mkmatlock/spectrometer/images/cfl_reference_with_labels.png

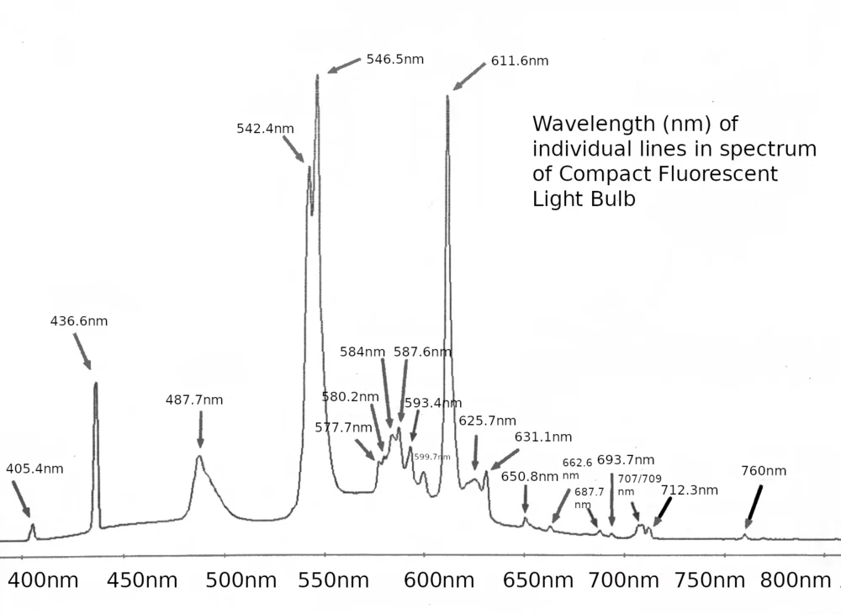
images/cfl_reference_with_labels.png
