mkmatlock/spectrometer/images/second order.png

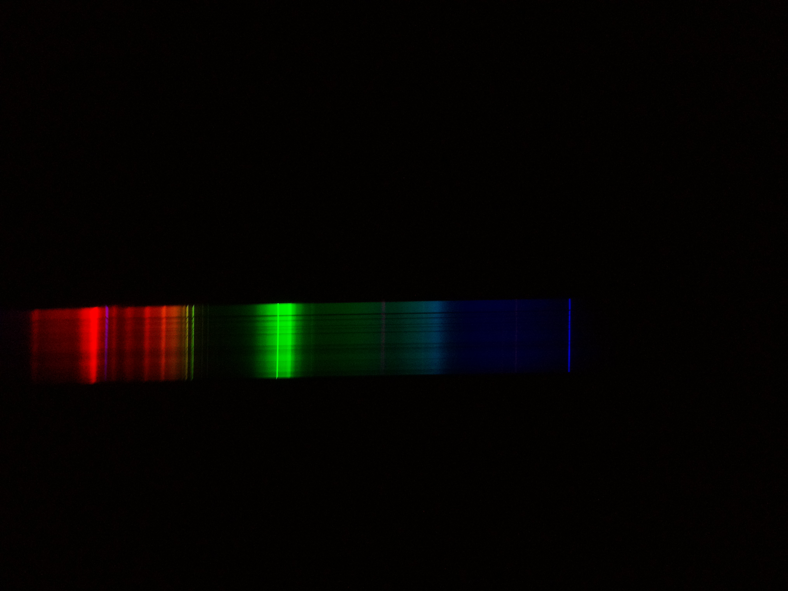
images/second order.png
