mkmatlock/spectrometer/models/Slit Stabilizer.3mf

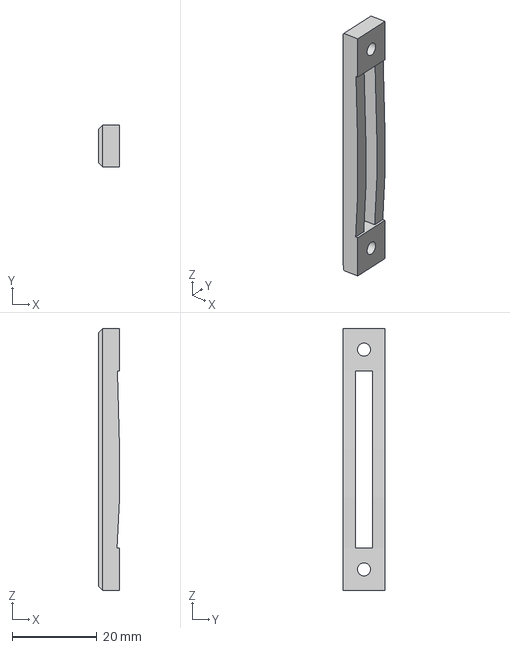
[picture p22: CAD file, 2026-09-16]
models/Slit Stabilizer.3mf
5.00 x 10.0 x 62.0 mm
