mkmatlock/spectrometer/models/Slit Mount.3mf

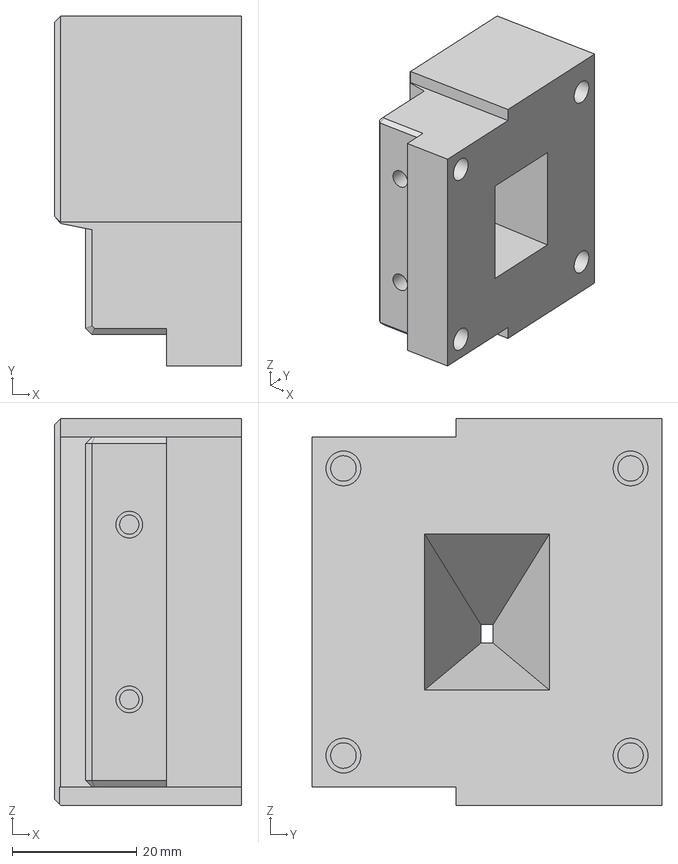
[picture p23: CAD file, 2026-09-16]
models/Slit Mount.3mf
30.0 x 56.0 x 62.0 mm
