mkmatlock/spectrometer/models/Microcontroller.3mf

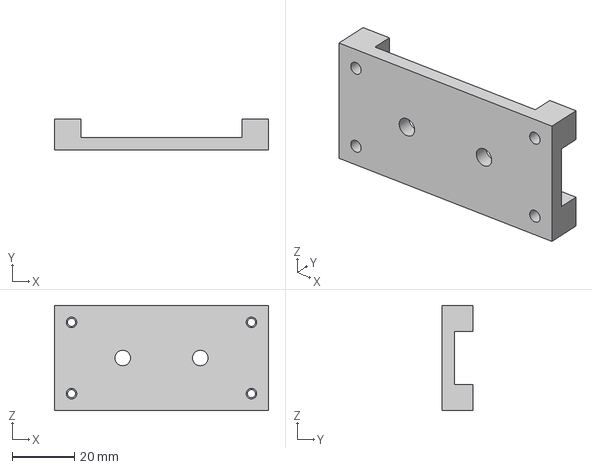
[picture p24: CAD file, 2026-09-16]
models/Microcontroller.3mf
69.0 x 10.0 x 34.0 mm
