mkmatlock/spectrometer/models/Interface.3mf

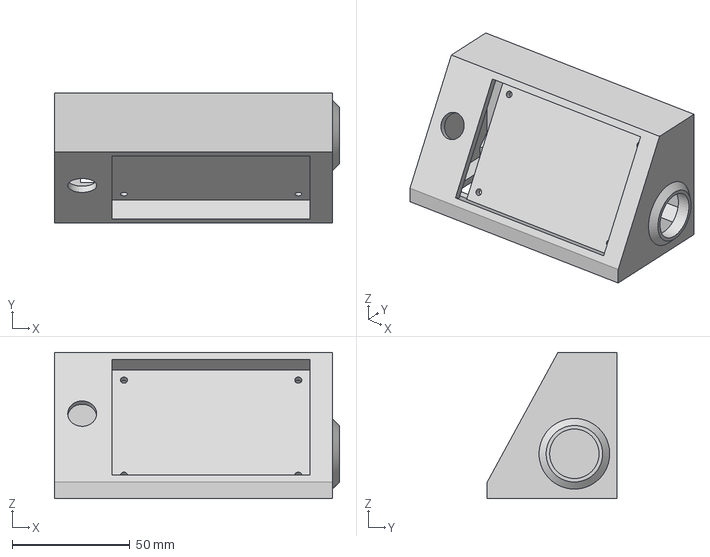
[picture p25: CAD file, 2026-09-16]
models/Interface.3mf
121.0 x 55.0 x 62.0 mm
