mkmatlock/spectrometer/images/build_bottom.jpg

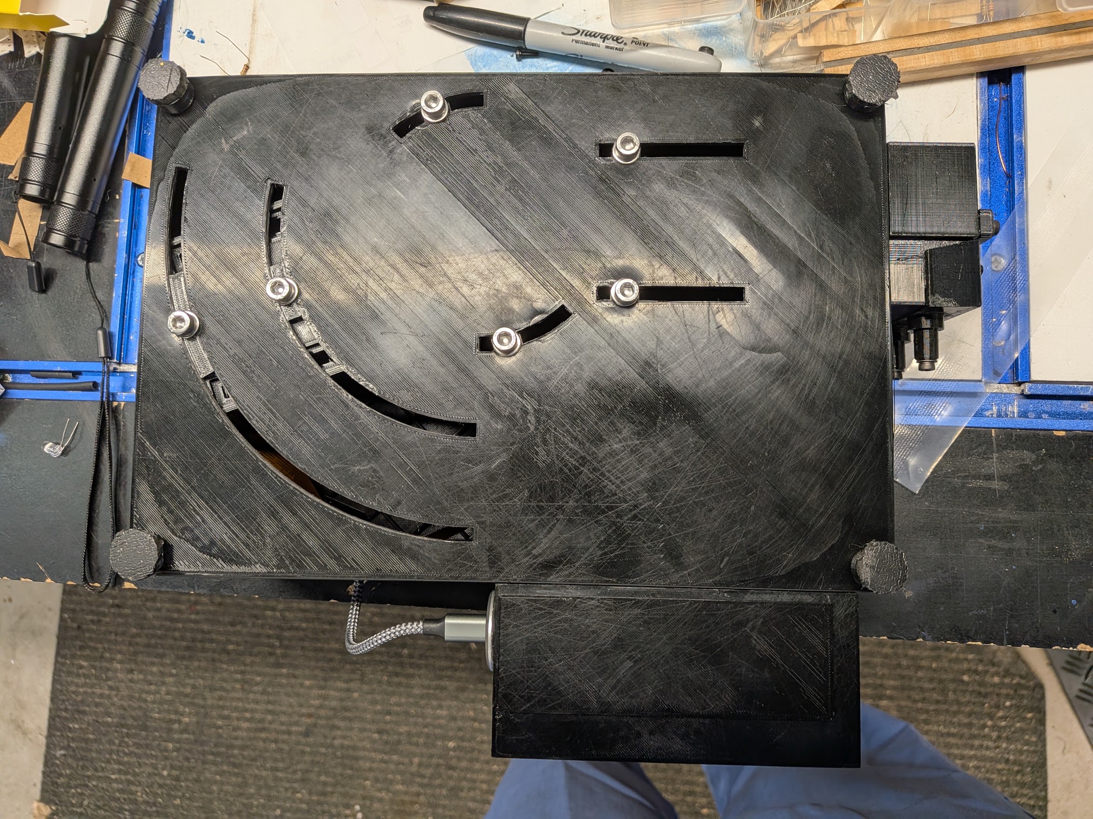
images/build_bottom.jpg
