mkmatlock/spectrometer/images/build_inside.jpg

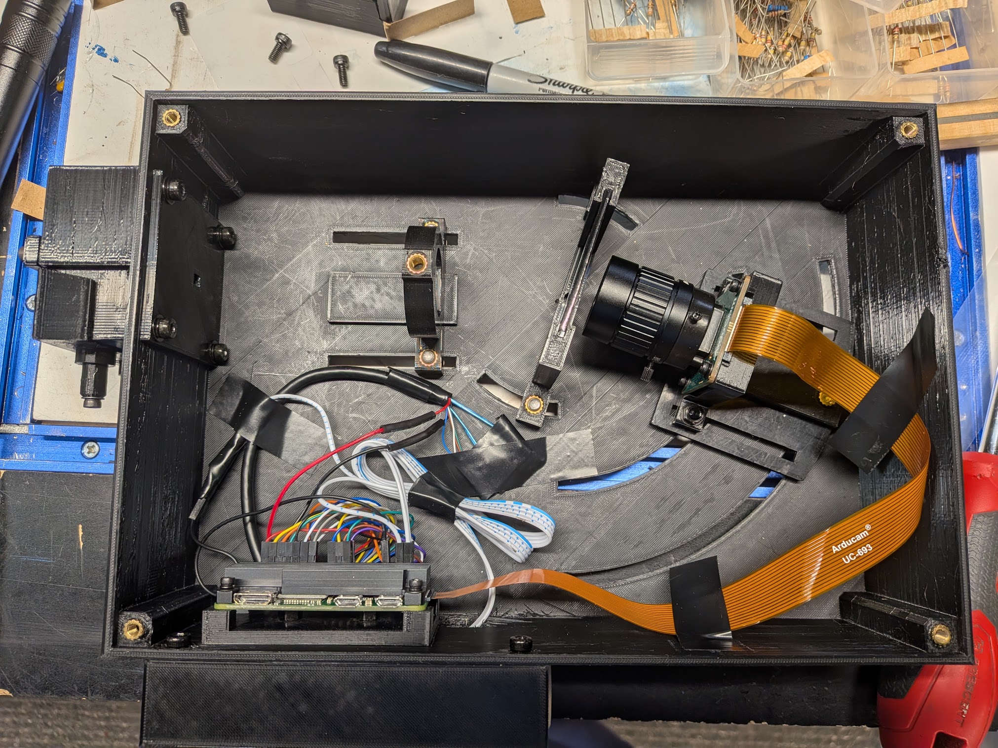
images/build_inside.jpg
