mkmatlock/spectrometer/images/build_lid_inside.jpg

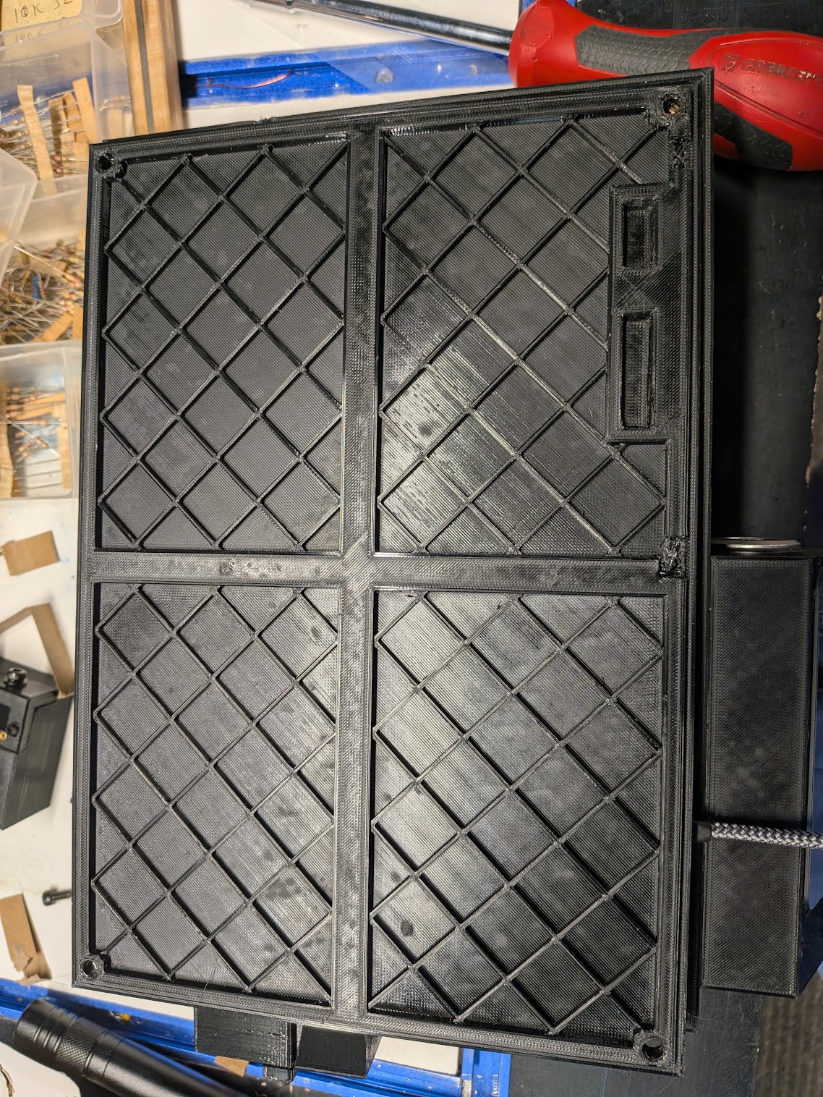
images/build_lid_inside.jpg
