mkmatlock/spectrometer/images/build_ports.jpg

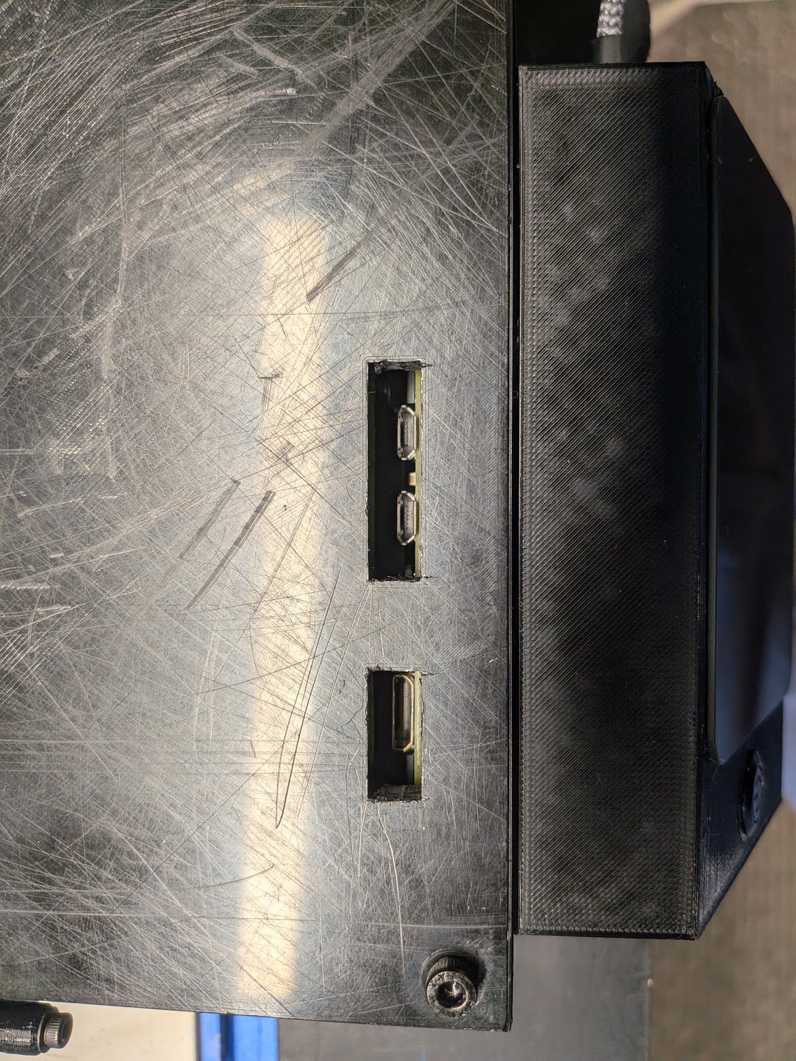
images/build_ports.jpg
