mkmatlock/spectrometer/images/build_slit.jpg

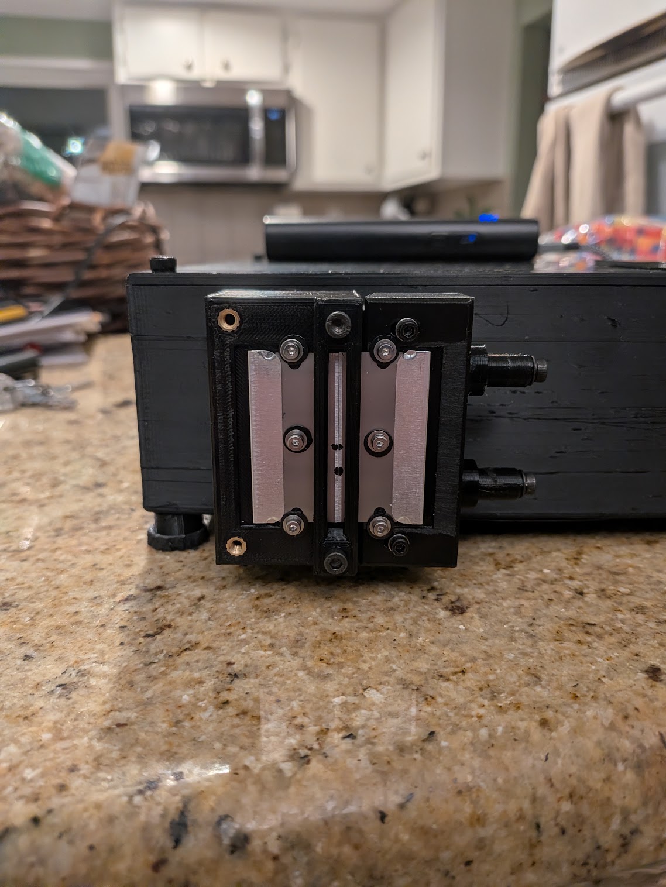
images/build_slit.jpg
