mkmatlock/spectrometer/tests/test_settings.py

import unittest
from unittest.mock import Mock, patch

from spectrometer.camera import CameraStream
from spectrometer.settings import SettingsView, network_status
from spectrometer.ui import SpectrometerUI


class SettingsTests(unittest.TestCase):
    def test_network_values_and_missing_tools(self):
        with patch('spectrometer.settings._output', side_effect=['192.168.1.42 fe80::1', 'Lab WiFi']):
            self.assertEqual(network_status(), ('192.168.1.42', 'Lab WiFi'))
        with patch('spectrometer.settings._output', side_effect=['192.168.1.42', None, '*:Lab:WiFi']):
            self.assertEqual(network_status(), ('192.168.1.42', 'Lab:WiFi'))
        with patch('spectrometer.settings._output', return_value=None):
            self.assertEqual(network_status(), ('Unavailable', 'Not connected / unavailable'))

    def test_settings_navigation_and_background_network(self):
        camera = Mock()
        camera.settings_snapshot.return_value = {'frame_rate': 5.0, 'resolution': (4056, 3040),
                                                 'exposure_us': 20000, 'frame_averaging': 3}
        ui = SpectrometerUI(camera=camera)
        try:
            with patch('spectrometer.settings.network_status', return_value=('10.0.0.2', 'Lab')):
                ui._open_settings()
                ui.settings_view.future.result(timeout=5)
                ui._poll_settings()
            self.assertEqual(ui.mode, 'settings')
            self.assertEqual(ui.settings_view.rows, [('Frame rate', '5 fps'),
                             ('Camera resolution', '4056 x 3040'), ('Exposure time', '20 ms'),
                             ('Frame averaging', '3'),
                             ('IP address', '10.0.0.2'), ('Wi-Fi network', 'Lab')])
            self.assertFalse(ui._poll_camera())
            ui._pointer_event('lcd', (40, 50), True)
            ui._pointer_event('lcd', (40, 50), False)
            self.assertEqual(ui.mode, 'settings')
            self.assertEqual(ui._settings_dialog, 'frame_rate')
            ui.buttons[1][2]()
            ui.buttons[0][2]()
            self.assertTrue(ui._calibration_dialog)
            ui.buttons[1][2]()
            self.assertEqual(ui.mode, 'settings')
            ui.buttons[1][2]()
            self.assertEqual(ui.mode, 'live')
            camera.request_pause.assert_called_once_with()
            camera.request_resume.assert_called_once_with()
        finally:
            ui.review.close()
            ui.settings_view.close()

    def test_edit_camera_settings_and_reconfigure_on_exit(self):
        camera = Mock()
        changes = []
        calibration = {'scale': {100: 500.0}, 'sensor_area': (0, 100, 1000, 200),
                       'channel_ranges': {'Red': (0, 999)}}
        ui = SpectrometerUI(
            camera=camera,
            camera_settings={'frame_rate': 5.0, 'resolution': (4056, 3040),
                             'exposure_us': None, 'frame_averaging': 3},
            calibration_settings=calibration,
            on_camera_settings_changed=lambda values, calibration=None:
            changes.append((values.copy(), calibration)))
        try:
            with patch('spectrometer.settings.network_status', return_value=('10.0.0.2', 'Lab')):
                ui._open_settings()

            ui._edit_setting(0)
            self.assertEqual((ui._settings_min, ui._settings_max), (-3, 5))
            ui._settings_value = 5
            ui._accept_setting()

            ui._edit_setting(2)
            self.assertEqual((ui._settings_min, ui._settings_max), (0, 201))
            ui._settings_value = 25
            ui._accept_setting()

            ui._edit_setting(3)
            self.assertEqual((ui._settings_min, ui._settings_max), (1, 10))
            ui._settings_value = 10
            ui._accept_setting()

            ui._edit_setting(1)
            ui._resolution_selected = 1
            ui._accept_setting()
            self.assertEqual(ui._camera_settings['resolution'], (2028, 1520))
            self.assertEqual(ui.calibration_settings,
                             {'scale': {}, 'sensor_area': (0, 0, 2028, 1520),
                              'channel_ranges': {}})
            self.assertEqual(ui.settings_view.rows[0:4],
                             [('Frame rate', '5 fps'),
                              ('Camera resolution', '2028 x 1520'),
                              ('Exposure time', '25 ms'), ('Frame averaging', '10')])

            ui._exit_settings()
            configured = camera.request_reconfigure.call_args.args[0]
            self.assertEqual(configured.resolution, (2028, 1520))
            self.assertEqual(configured.roi, (0, 0, 2028, 1520))
            self.assertEqual(configured.frame_averaging, 10)
            self.assertEqual(len(changes), 4)
            camera.request_resume.assert_not_called()
        finally:
            ui.review.close()
            ui.settings_view.close()

    def test_slow_frame_rates_round_trip_and_exposure_limit(self):
        ui = SpectrometerUI()
        try:
            for seconds in (2, 3, 4, 5):
                ui._edit_setting(0)
                track = ui._setting_slider_rect()
                position = 2 - seconds
                x = track.left + (position - ui._settings_min) / (ui._settings_max - ui._settings_min) * track.width
                ui._set_slider_position((x, track.centery))
                ui._accept_setting()
                self.assertAlmostEqual(ui._camera_settings['frame_rate'], 1 / seconds)
                self.assertEqual(ui.settings_view.rows[0], ('Frame rate', f'{seconds} spf'))
                ui._edit_setting(0)
                self.assertEqual(ui._settings_value, position)
                ui._cancel_setting()
                ui._edit_setting(2)
                self.assertEqual(ui._settings_max, seconds * 1000 + 1)
                ui._cancel_setting()
        finally:
            ui.review.close()
            ui.settings_view.close()

    def test_exposure_modes_and_fixed_values_across_frame_rates(self):
        camera = Mock()
        camera.exposure_limits.side_effect = lambda fps, resolution: (114, min(900000, int(1000000 / fps)))
        from spectrometer.config import DEFAULTS
        ui = SpectrometerUI(camera=camera, camera_settings=DEFAULTS['camera'])
        try:
            def change_rate(position):
                ui._edit_setting(0)
                ui._settings_value = position
                ui._accept_setting()

            for mode in ('min', 'max'):
                ui._edit_setting(2)
                ui._settings_value = ui._exposure_options.index(mode)
                ui._accept_setting()
                for position in (1, 5, -3):
                    change_rate(position)
                    self.assertEqual(ui._camera_settings['exposure_us'], mode)
                    self.assertEqual(ui.settings_view.rows[2], ('Exposure time', mode.title()))
                    ui._edit_setting(2)
                    self.assertEqual(ui._exposure_options[ui._settings_value], mode)
                    ui._cancel_setting()

            for previous, expected in ((25000, 25000), (500000, 200000), (10, 114)):
                ui._camera_settings['exposure_us'] = previous
                change_rate(5)
                self.assertEqual(ui._camera_settings['exposure_us'], expected)
                change_rate(1)
                self.assertEqual(ui._camera_settings['exposure_us'], expected)
                # Opening and accepting must preserve exact microseconds.
                ui._edit_setting(2)
                ui._accept_setting()
                self.assertEqual(ui._camera_settings['exposure_us'], expected)
        finally:
            ui.review.close()
            ui.settings_view.close()

    def test_snapshot_uses_actual_frame_timing_and_exposure(self):
        camera = CameraStream()
        try:
            camera._frame_duration_us = 250000
            camera._exposure_us = 12345
            self.assertEqual(camera.settings_snapshot(), {'frame_rate': 4.0,
                             'resolution': (4056, 3040), 'exposure_us': 12345,
                             'frame_averaging': 3})
        finally:
            camera.close()

    def test_calibration_dialog_selection_and_modal_input(self):
        ui = SpectrometerUI()
        try:
            with patch('spectrometer.settings.network_status', return_value=('Unavailable', 'Unavailable')):
                ui._open_settings()
                ui.settings_view.future.result(timeout=5)
            ui._calibrate()
            self.assertEqual([b[0] for b in ui.buttons], ['Select', 'Back'])
            self.assertEqual([r[0] for r in ui._calibration_rows],
                             ['Background', 'Sensor', 'Scale', 'Channel'])
            ui._select_calibration()
            self.assertIn('Choose', ui._calibration_message)
            for index, (name, rect) in enumerate(ui._calibration_rows[:1]):
                ui._pointer_event('lcd', rect.center, True)
                ui._pointer_event('lcd', rect.center, False)
                self.assertEqual(ui._calibration_selected, index)
                ui._select_calibration()
                self.assertEqual(ui._calibration_message, name + ': not implemented yet')
            ui._pointer_event('lcd', (350, 300), True)
            ui._pointer_event('lcd', (350, 300), False)
            self.assertTrue(ui._calibration_dialog)  # Underlying Settings Back is blocked.
            ui._back_calibration()
            self.assertFalse(ui._calibration_dialog)
            self.assertEqual(ui.mode, 'settings')
            self.assertEqual([b[0] for b in ui.buttons], ['Calibrate', 'Back'])
        finally:
            ui.review.close()
            ui.settings_view.close()
