mkmatlock/spectrometer/tests/test_review.py

from datetime import datetime, timezone
from pathlib import Path
import pickle
from copy import deepcopy
import tempfile
import unittest
from unittest.mock import Mock, patch

import numpy as np
import pygame

from spectrometer.camera import BAR_SIZE
from spectrometer.capture import save_capture
from spectrometer.review import ReviewList, load_spectrum, raw_rgb
from spectrometer.ui import SpectrometerUI
from tests.spectrum_fixtures import spectrum_record


def record(second=0):
    return spectrum_record(
        timestamp=datetime(2026, 9, 12, 12, 0, second, tzinfo=timezone.utc),
        spectrum_intensity=np.arange(3500, dtype=np.int32),
        spectrum_bar=bytes((255, 0, 0)) * (BAR_SIZE[0] * BAR_SIZE[1]))


class ReviewTests(unittest.TestCase):
    def test_delete_modal_cancel_confirm_and_exact_loaded_file(self):
        with tempfile.TemporaryDirectory() as directory:
            older = save_capture(record(0), directory)
            newest = save_capture(record(1), directory)
            ui = SpectrometerUI(review_directory=directory)
            try:
                ui._open_review()
                ui.review.selected = 0
                ui.review.display()
                ui.review.future.result(timeout=5)
                ui.review.selected = 1  # Selection changes must not change delete target.
                ui._poll_review()
                def tap(position):
                    ui._pointer_event('lcd', position, True)
                    ui._pointer_event('lcd', position, False)
                tap((80, 280))
                self.assertTrue(ui._delete_dialog)
                self.assertTrue(newest.exists())
                tap((350, 280))  # Back behind the modal must not receive input.
                self.assertTrue(ui._delete_dialog)
                tap((330, 190))
                self.assertFalse(ui._delete_dialog)
                self.assertEqual(ui.mode, 'saved')
                self.assertTrue(newest.exists())
                tap((80, 280))
                tap((150, 190))
                self.assertFalse(newest.exists())
                self.assertTrue(older.exists())
                self.assertEqual(ui.mode, 'review')
                self.assertFalse(ui._delete_dialog)
                self.assertEqual(ui.review.entries, [older])
            finally:
                ui.review.close()
                ui.settings_view.close()

    def test_delete_failure_keeps_file_and_dialog_open(self):
        with tempfile.TemporaryDirectory() as directory:
            path = save_capture(record(), directory)
            ui = SpectrometerUI(review_directory=directory)
            try:
                ui._open_review()
                ui.review.selected = 0
                ui.review.display()
                ui.review.future.result(timeout=5)
                ui._poll_review()
                ui._ask_delete()
                with patch.object(Path, 'unlink', side_effect=PermissionError('Read only')):
                    ui._confirm_delete()
                self.assertTrue(path.exists())
                self.assertTrue(ui._delete_dialog)
                self.assertIn('Delete failed', ui._delete_message)
            finally:
                ui.review.close()
                ui.settings_view.close()

    def test_newest_first_scroll_and_empty_list(self):
        with tempfile.TemporaryDirectory() as directory:
            review = ReviewList(directory)
            try:
                review.refresh()
                self.assertEqual(review.entries, [])
                review.display()
                self.assertEqual(review.message, 'Select a capture first')
                for second in range(8):
                    save_capture(record(second), directory)
                review.refresh()
                self.assertTrue(review.entries[0].name.endswith('07.pkl'))
                review.scroll(100)
                self.assertEqual(review.offset, 3)
                review.scroll(-100)
                self.assertEqual(review.offset, 0)
            finally:
                review.close()

    def test_select_display_back_exit_and_live_isolation(self):
        with tempfile.TemporaryDirectory() as directory:
            save_capture(record(), directory)
            camera = Mock()
            ui = SpectrometerUI(camera=camera, review_directory=directory)
            try:
                original = ui._plot
                ui._open_review()
                camera.request_pause.assert_called_once()
                self.assertFalse(ui._poll_camera())
                camera.poll.assert_not_called()
                ui._pointer_event('lcd', (50, 50), True)
                ui._pointer_event('lcd', (50, 50), False)
                ui.buttons[0][2]()
                ui.review.future.result(timeout=5)
                ui._poll_review()
                self.assertEqual(ui.mode, 'saved')
                self.assertEqual([b[0] for b in ui.buttons], ['Delete', 'Modes', 'Back'])
                self.assertEqual(ui._camera_bar.get_at((0, 0))[:3], (255, 0, 0))
                ui.buttons[2][2]()
                self.assertEqual(ui.mode, 'review')
                self.assertEqual(ui.review.selected, 0)
                ui.buttons[2][2]()
                self.assertEqual(ui.mode, 'live')
                self.assertIs(ui._plot, original)
                camera.request_resume.assert_called_once()
            finally:
                ui.review.close()

    def test_swipe_scroll_does_not_select(self):
        ui = SpectrometerUI()
        try:
            ui._open_review()
            ui.review.entries = [Path(str(i)) for i in range(12)]
            ui._pointer_event('lcd', (50, 220), True)
            ui._pointer_motion('lcd', (50, 90))
            ui._pointer_event('lcd', (50, 90), False)
            self.assertEqual(ui.review.offset, 3)
            self.assertIsNone(ui.review.selected)
        finally:
            ui.review.close()

    def test_bad_pickle_shows_error_and_stays_in_list(self):
        with tempfile.TemporaryDirectory() as directory:
            path = Path(directory) / 'spectrum-broken.pkl'
            path.write_bytes(b'broken')
            review = ReviewList(directory)
            try:
                review.refresh()
                review.selected = 0
                review.display()
                try:
                    review.future.result(timeout=5)
                except Exception:
                    pass
                self.assertIsNone(review.poll())
                self.assertTrue(review.message.startswith('Cannot load:'))
            finally:
                review.close()

    def test_averaged_bgr_roi_decodes_without_changing_saved_image(self):
        data = record()
        data['averaged_camera_output'][:] = (10, 20, 30)
        result = raw_rgb(data)
        self.assertEqual(result.shape, (250, 3500, 3))
        np.testing.assert_array_equal(result[0, 0], [30, 20, 10])
        np.testing.assert_array_equal(data['averaged_camera_output'][0, 0], [10, 20, 30])

    def test_invalid_spectrum_rejected(self):
        with tempfile.TemporaryDirectory() as directory:
            data = record()
            data['spectrum_intensity'] = np.zeros(10)
            path = save_capture(data, directory)
            with self.assertRaises(ValueError):
                load_spectrum(path)

    def test_plot_requires_saved_roi_bar_maximum_and_nested_calibration(self):
        data = spectrum_record(spectrum_roi=(0, 0, 462, 2))
        fields = [('spectrum_roi',), ('spectrum_bar',), ('spectrum_maximum',),
                  ('instrument_settings', 'calibration_settings')]
        with tempfile.TemporaryDirectory() as directory:
            path = Path(directory) / 'spectrum-test.pkl'
            for field in fields:
                with self.subTest(field=field):
                    invalid = deepcopy(data)
                    target = invalid
                    for part in field[:-1]:
                        target = target[part]
                    del target[field[-1]]
                    path.write_bytes(pickle.dumps(invalid))
                    with self.assertRaises(KeyError):
                        load_spectrum(path)

    def test_channel_processing_requires_averaged_roi_metadata(self):
        data = spectrum_record(spectrum_roi=(0, 0, 462, 2))
        fields = [('averaged_camera_output',),
                  ('instrument_settings', 'averaged_camera_format'),
                  ('instrument_settings', 'averaged_camera_format', 'size'),
                  ('instrument_settings', 'averaged_camera_format', 'origin'),
                  ('instrument_settings', 'averaged_camera_format', 'format')]
        for field in fields:
            with self.subTest(field=field):
                invalid = deepcopy(data)
                target = invalid
                for part in field[:-1]:
                    target = target[part]
                del target[field[-1]]
                with self.assertRaises(KeyError):
                    raw_rgb(invalid)

    def test_saved_maximum_controls_plot_independently_of_calculation_metadata(self):
        values = np.zeros(462, np.int32)
        values[100] = 500
        data = spectrum_record(spectrum_roi=(0, 0, 462, 2),
                               spectrum_intensity=values, spectrum_maximum=500)
        with tempfile.TemporaryDirectory() as directory:
            path = Path(directory) / 'spectrum-test.pkl'
            ui = SpectrometerUI(review_directory=directory)
            try:
                ui.mode = 'saved'
                for calculation in ('rgb_channel_sum', 'unrecognized', None):
                    with self.subTest(calculation=calculation):
                        if calculation is None:
                            data['instrument_settings'].pop('intensity_calculation')
                        else:
                            data['instrument_settings']['intensity_calculation'] = calculation
                        path.write_bytes(pickle.dumps(data))
                        frame = load_spectrum(path)
                        ui._update_plot(frame)
                        self.assertEqual(frame.maximum, 500)
                        self.assertEqual(ui._plot.maximum, 500)
                        self.assertEqual(min(point[1] for point in ui._plot.points),
                                         ui._plot.AREA.top)
                        np.testing.assert_array_equal(frame.intensity, values)
            finally:
                ui.review.close()
                ui.settings_view.close()
