mkmatlock/spectrometer/tests/test_scale.py

import pickle
from copy import deepcopy
from pathlib import Path
import tempfile
import unittest
from unittest.mock import Mock, patch

import numpy as np
import pygame

from spectrometer.scale import PeakSelection, peak_indices
from spectrometer.config import DEFAULTS, SettingsStore
from spectrometer.ui import SpectrometerUI
from tests.spectrum_fixtures import spectrum_record


class ScaleTests(unittest.TestCase):
    def test_reset_requires_confirmation_and_only_clears_draft(self):
        with tempfile.TemporaryDirectory() as directory:
            store = SettingsStore(Path(directory) / '.spectrometer_config')
            store.update(calibration={'scale': {1000: 500.0, 2500: 700.0}})
            ui = SpectrometerUI(
                calibration_settings=deepcopy(store.data['calibration']),
                on_calibration_changed=lambda data: store.update(calibration=data))
            try:
                ui.mode = 'saved'
                ui._scale_active = True
                ui._saved_buttons = []
                original = deepcopy(ui.calibration_settings)
                ui._reset_scale()
                self.assertTrue(ui._scale_reset_dialog)
                self.assertEqual(ui._scale_labels, original['scale'])
                with patch.object(ui, '_select_peak') as select:
                    ui._pointer_event('lcd', (100, 100), True)
                    ui._pointer_event('lcd', (100, 100), False)
                    select.assert_not_called()
                ui._cancel_scale_reset()
                self.assertFalse(ui._scale_reset_dialog)
                self.assertEqual(ui._scale_labels, original['scale'])
                self.assertIs(ui.buttons, ui._saved_buttons)
                ui._reset_scale()
                ui._confirm_scale_reset()
                self.assertFalse(ui._scale_reset_dialog)
                self.assertEqual(ui._scale_labels, {})
                self.assertEqual(ui.calibration_settings, original)
                self.assertEqual(SettingsStore(store.path).data['calibration'], original)
            finally:
                ui.review.close()
                ui.settings_view.close()

    def test_absorption_plateau_valleys_and_toggle_in_scale(self):
        np.testing.assert_array_equal(peak_indices([9, 2, 2, 2, 9, 3, 9], absorption=True), [2, 5])
        ui = SpectrometerUI()
        try:
            ui.mode = 'saved'
            ui._scale_active = True
            values = np.full(3500, 50000, dtype=np.int32)
            values[1200] = 10000
            ui._plot.update(values)
            ui._reset_peaks(values)
            ui._saved_buttons = [('Accept', pygame.Rect(8, 264, 110, 48), ui._finish_scale),
                                 ('Reset', pygame.Rect(126, 264, 110, 48), ui._reset_scale),
                                 ('Modes', pygame.Rect(244, 264, 110, 48), ui._ask_filter),
                                 ('Back', pygame.Rect(362, 264, 110, 48), ui._cancel_scale)]
            ui._ask_filter()
            ui._choose_filter('Emission')
            self.assertEqual(ui.buttons[3][0], 'Absorption')
            self.assertTrue(ui._filter_dialog)
            np.testing.assert_array_equal(ui._peaks.indices, [1200])
            ui._back_filter()
            ui._select_peak(ui._peaks.positions[0])
            self.assertEqual(ui._peak_message, 'Pixel 1200')
            self.assertEqual([b[0] for b in ui.buttons], ['Label', 'Back'])
            ui._back_peak()
            self.assertEqual([b[0] for b in ui.buttons], ['Accept', 'Reset', 'Modes', 'Back'])
            ui._ask_filter()
            ui._choose_filter('Absorption')
            self.assertFalse(ui._absorption)
            self.assertIsNone(ui._peaks.marker)
        finally:
            ui.review.close()
            ui.settings_view.close()

    def test_plateaus_and_flat_spectra(self):
        np.testing.assert_array_equal(peak_indices([0, 2, 2, 2, 0, 3, 0]), [2, 5])
        self.assertEqual(len(peak_indices(np.zeros(3500))), 0)
        self.assertEqual(len(peak_indices(np.arange(3500))), 0)

    def test_nearest_peak_uses_screen_distance(self):
        values = np.zeros(3500)
        values[1000], values[2500] = 50000, 30000
        peaks = PeakSelection(values, pygame.Rect(9, 36, 462, 130), 63750)
        self.assertEqual(peaks.select(peaks.positions[1] + (2, 4)), 2500)
        self.assertEqual(peaks.marker, tuple(np.rint(peaks.positions[1]).astype(int)))

    def test_scale_capture_selection_peak_dialog_and_return(self):
        with tempfile.TemporaryDirectory() as directory:
            path = Path(directory) / 'spectrum-2026-09-13-12-00-00.pkl'
            values = np.zeros(3500, dtype=np.int32)
            values[1000], values[2500] = 50000, 30000
            original = pickle.dumps(spectrum_record(spectrum_intensity=values))
            path.write_bytes(original)
            camera = Mock()
            camera.settings_snapshot.return_value = deepcopy(DEFAULTS['camera'])
            ui = SpectrometerUI(camera=camera, review_directory=directory)
            try:
                with patch('spectrometer.settings.network_status', return_value=('Unavailable', 'Unavailable')):
                    ui._open_settings()
                    ui.settings_view.future.result(timeout=5)
                ui._calibrate()
                ui._calibration_selected = 2
                ui._select_calibration()
                self.assertEqual(ui.mode, 'review')
                self.assertTrue(ui._scale_active)
                self.assertFalse(ui._calibration_dialog)
                ui.review.selected = 0
                ui.review.display()
                ui.review.future.result(timeout=5)
                ui._poll_review()
                self.assertEqual(ui.mode, 'saved')
                self.assertEqual([b[0] for b in ui.buttons], ['Accept', 'Reset', 'Modes', 'Back'])
                position = tuple(ui._peaks.positions[0] + (2, 2))
                ui._pointer_event('lcd', position, True)
                ui._pointer_event('lcd', position, False)
                self.assertTrue(ui._peak_dialog)
                self.assertIn('1000', ui._peak_message)
                self.assertEqual([b[0] for b in ui.buttons], ['Label', 'Back'])
                ui._label_peak()
                self.assertTrue(ui._keypad_open)
                ui._cancel_label()
                ui._back_peak()
                self.assertIsNone(ui._peaks.marker)
                self.assertEqual(ui.mode, 'saved')
                self.assertFalse(ui._peak_dialog)
                ui._review_list()
                ui._exit_review()
                self.assertEqual(ui.mode, 'settings')
                self.assertFalse(ui._scale_active)
                camera.request_resume.assert_not_called()
                self.assertEqual(path.read_bytes(), original)
            finally:
                ui.review.close()
                ui.settings_view.close()
