mkmatlock/spectrometer/tests/test_config.py

from copy import deepcopy
from pathlib import Path
import pickle
import tempfile
import unittest
from unittest.mock import Mock, patch

import numpy as np

from spectrometer.config import DEFAULTS, SettingsStore
from spectrometer.camera import process_frame
from spectrometer.review import load_spectrum
from spectrometer.ui import SpectrometerUI
from tests.spectrum_fixtures import spectrum_record


class ConfigTests(unittest.TestCase):
    def setUp(self):
        self.directory = tempfile.TemporaryDirectory()
        self.addCleanup(self.directory.cleanup)
        self.path = Path(self.directory.name) / '.spectrometer_config'

    def test_defaults_and_round_trip(self):
        store = SettingsStore(self.path)
        self.assertEqual(pickle.loads(self.path.read_bytes()), DEFAULTS)
        store.update(camera={'frame_rate': 4, 'exposure_us': 20000,
                             'resolution': (2028, 1520)},
                     calibration={'scale': {100: 532.1}, 'sensor_area': (0, 100, 2000, 200),
                                  'channel_ranges': {'Red': (100, 1900)}})
        self.assertEqual(SettingsStore(self.path).data, store.data)
        self.assertEqual(store.data['calibration']['channel_ranges']['Red'], (100, 1900))
        self.assertEqual(DEFAULTS['calibration']['scale'], {})

    def test_exposure_modes_persist_when_frame_rate_changes(self):
        store = SettingsStore(self.path)
        for mode in ('min', 'max'):
            store.update(camera={'exposure_us': mode})
            store.update(camera={'frame_rate': 0.2})
            self.assertEqual(SettingsStore(self.path).data['camera']['exposure_us'], mode)

    def test_failed_write_preserves_previous_file_and_memory(self):
        store = SettingsStore(self.path)
        original = self.path.read_bytes()
        with patch('spectrometer.config.os.replace', side_effect=OSError('Disk full')):
            with self.assertRaises(OSError):
                store.update(camera={'frame_rate': 3})
        self.assertEqual(self.path.read_bytes(), original)
        self.assertEqual(store.data, DEFAULTS)
        self.assertEqual(list(self.path.parent.iterdir()), [self.path])

    def test_invalid_settings_and_corrupt_file_are_not_overwritten(self):
        store = SettingsStore(self.path)
        original = self.path.read_bytes()
        for changes in ({'frame_rate': 0}, {'exposure_us': -1}, {'resolution': None},
                        {'frame_averaging': 0}, {'frame_averaging': 11}):
            with self.assertRaises(ValueError):
                store.update(camera=changes)
        self.assertEqual(self.path.read_bytes(), original)
        self.path.write_bytes(b'broken pickle')
        with self.assertRaises(ValueError):
            SettingsStore(self.path)
        self.assertEqual(self.path.read_bytes(), b'broken pickle')

    def test_incomplete_settings_are_rejected_without_default_merging(self):
        for section, key in (('camera', 'frame_averaging'),
                             ('calibration', 'channel_ranges'),
                             ('calibration', 'sensor_area'),
                             ('calibration', 'scale')):
            data = deepcopy(DEFAULTS)
            del data[section][key]
            original = pickle.dumps(data)
            self.path.write_bytes(original)
            with self.assertRaises(ValueError):
                SettingsStore(self.path)
            self.assertEqual(self.path.read_bytes(), original)

    def test_label_accept_modify_and_delete_leave_persistent_settings_unchanged(self):
        store = SettingsStore(self.path)
        persist = Mock(side_effect=lambda data: store.update(calibration=data))
        ui = SpectrometerUI(calibration_settings=deepcopy(store.data['calibration']),
                            on_calibration_changed=persist)
        self.addCleanup(ui.review.close)
        self.addCleanup(ui.settings_view.close)
        values = np.zeros(3500, np.int32)
        values[1000] = 50000
        ui.mode = 'saved'
        ui._scale_active = True
        ui._saved_buttons = []
        ui._reset_peaks(values)
        for label in ('532.1', '532.2'):
            ui._select_peak(tuple(ui._peaks.positions[0]))
            ui._label_peak()
            ui._label_input = label
            ui._accept_label()
            self.assertEqual(ui._scale_labels, {1000: float(label)})
            self.assertEqual(SettingsStore(self.path).data['calibration']['scale'], {})
        ui._select_peak(tuple(ui._peaks.positions[0]))
        ui._delete_peak_label()
        self.assertEqual(ui._scale_labels, {})
        self.assertEqual(ui.calibration_settings['scale'], {})
        self.assertEqual(SettingsStore(self.path).data['calibration']['scale'], {})
        persist.assert_not_called()

    def test_custom_sensor_area_capture_review_and_peak_coordinates(self):
        roi = (100, 20, 600, 40)
        image = np.zeros((480, 640, 3), np.uint8)
        image[20:40, 200] = 255
        frame = process_frame(image, roi, (640, 480))
        self.assertEqual(frame.roi, roi)
        self.assertEqual(frame.intensity.shape, (500,))
        self.assertEqual(frame.intensity[100], 20 * 255 * 3)
        capture = self.path.parent / 'spectrum.pkl'
        capture.write_bytes(pickle.dumps(spectrum_record(
            spectrum_roi=roi, spectrum_bar=frame.bar, spectrum_intensity=frame.intensity,
            averaged_camera_output=image[20:40, 100:600].copy(),
            spectrum_maximum=frame.maximum)))
        loaded = load_spectrum(capture)
        ui = SpectrometerUI()
        self.addCleanup(ui.review.close)
        self.addCleanup(ui.settings_view.close)
        ui._update_plot(loaded)
        ui._reset_peaks(loaded.intensity)
        self.assertEqual(ui._plot.maximum, 20 * 255 * 3)
        self.assertEqual(ui._peaks.select(ui._peaks.positions[0]), 200)
